Antonio-Balestrino/Bluetooth-Speaker-Senior-Design/docs/Kicad Files/Power Distribution Jack/PD Jack_RevB/3D View Bottom.jpg

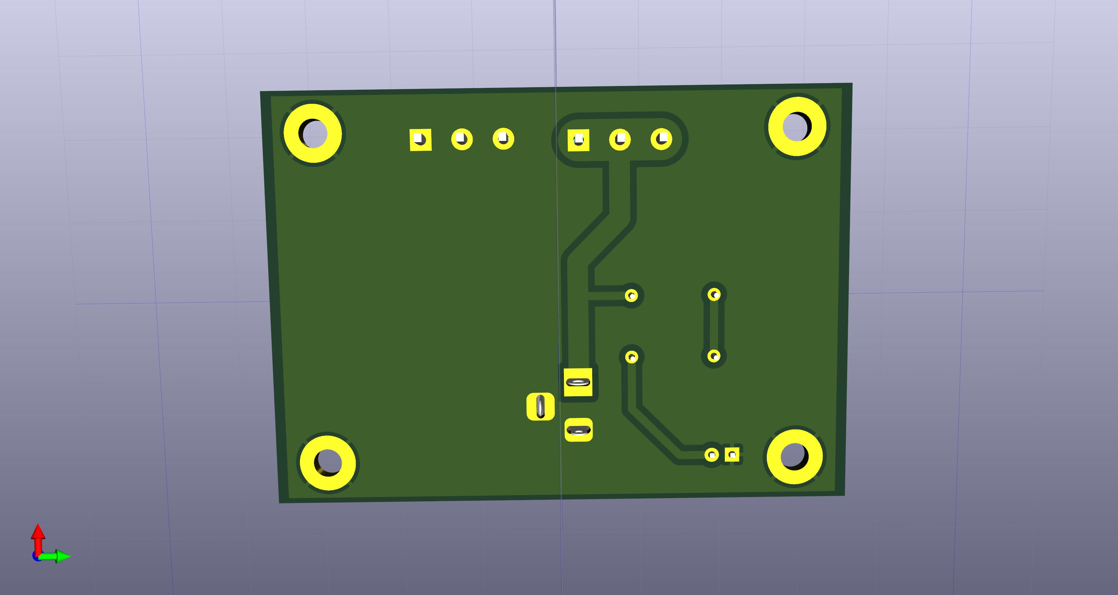
docs/Kicad Files/Power Distribution Jack/PD Jack_RevB/3D View Bottom.jpg
