Antonio-Balestrino/Bluetooth-Speaker-Senior-Design/docs/Pics/IMG_7961.JPG

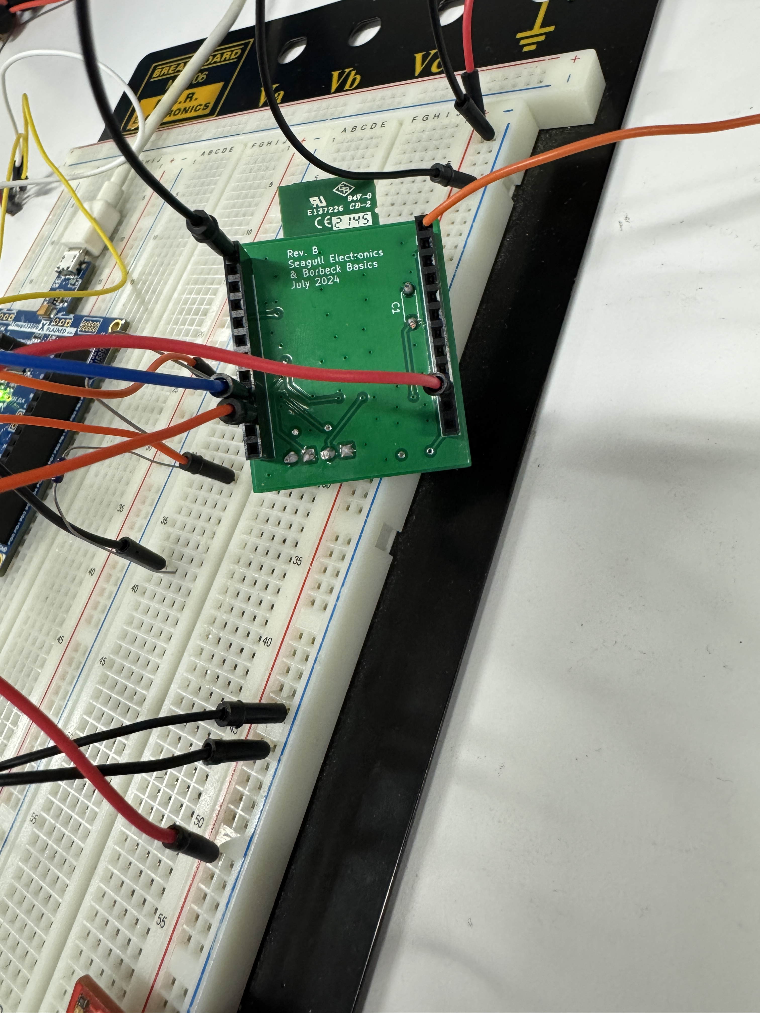
docs/Pics/IMG_7961.JPG
