Antonio-Balestrino/Bluetooth-Speaker-Senior-Design/docs/Pics/IMG_7962.JPG

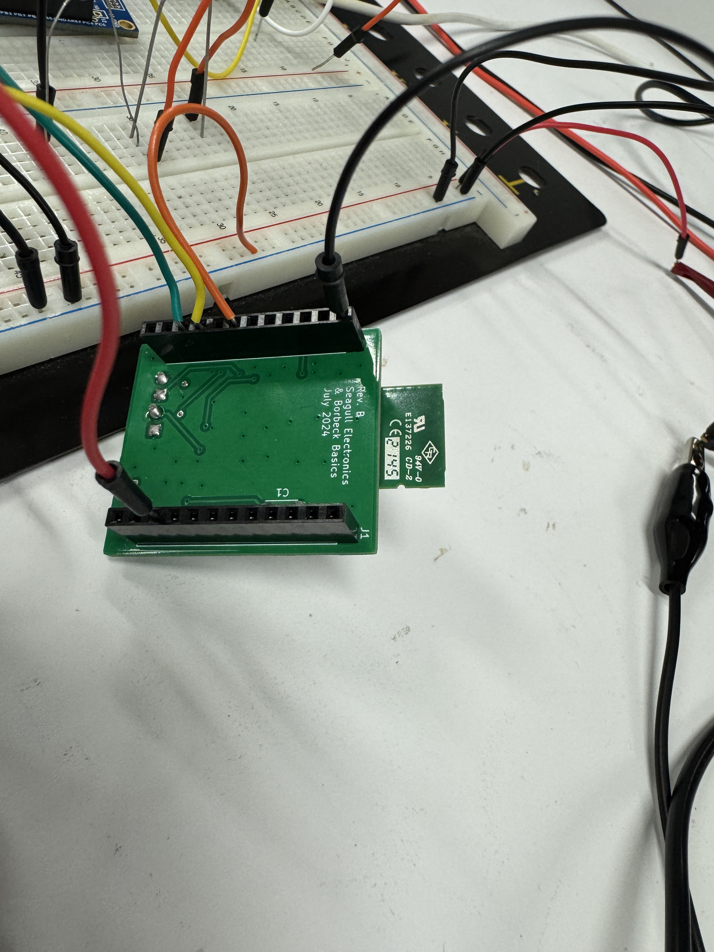
docs/Pics/IMG_7962.JPG
