Antonio-Balestrino/Bluetooth-Speaker-Senior-Design/docs/Pics/IMG_8013(1).JPG

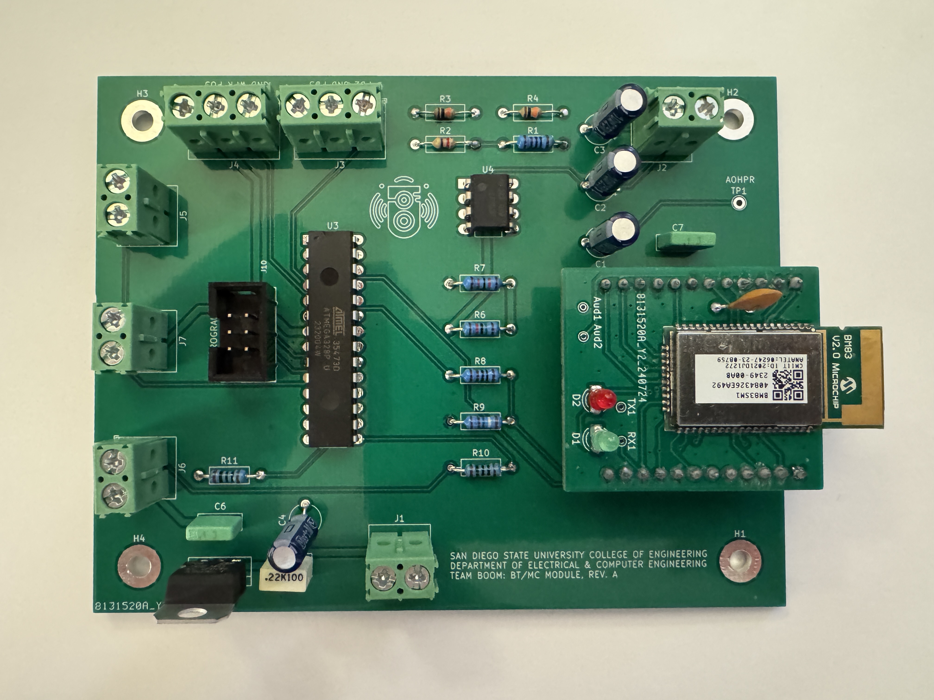
docs/Pics/IMG_8013(1).JPG
