Antonio-Balestrino/Bluetooth-Speaker-Senior-Design/docs/Pics/IMG_8014.JPG

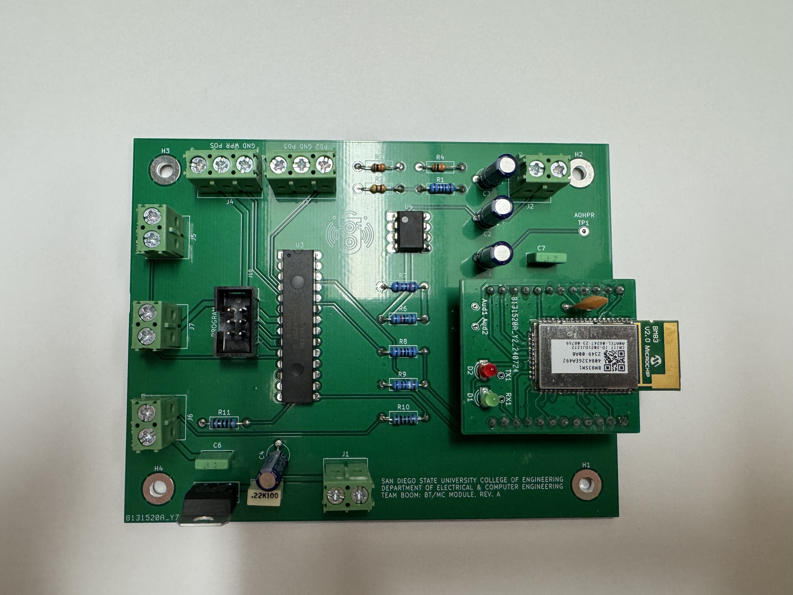
docs/Pics/IMG_8014.JPG
