Antonio-Balestrino/Bluetooth-Speaker-Senior-Design/docs/Pics/IMG_8023.JPG

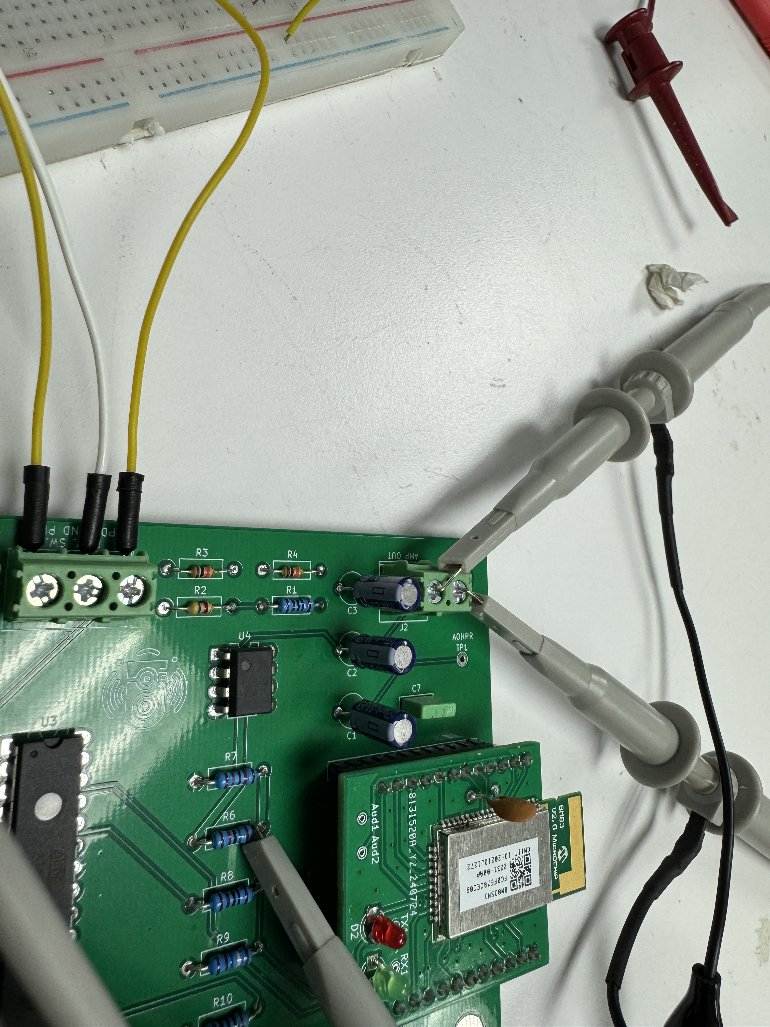
docs/Pics/IMG_8023.JPG
