Antonio-Balestrino/Bluetooth-Speaker-Senior-Design/docs/Pics/IMG_8121.JPG

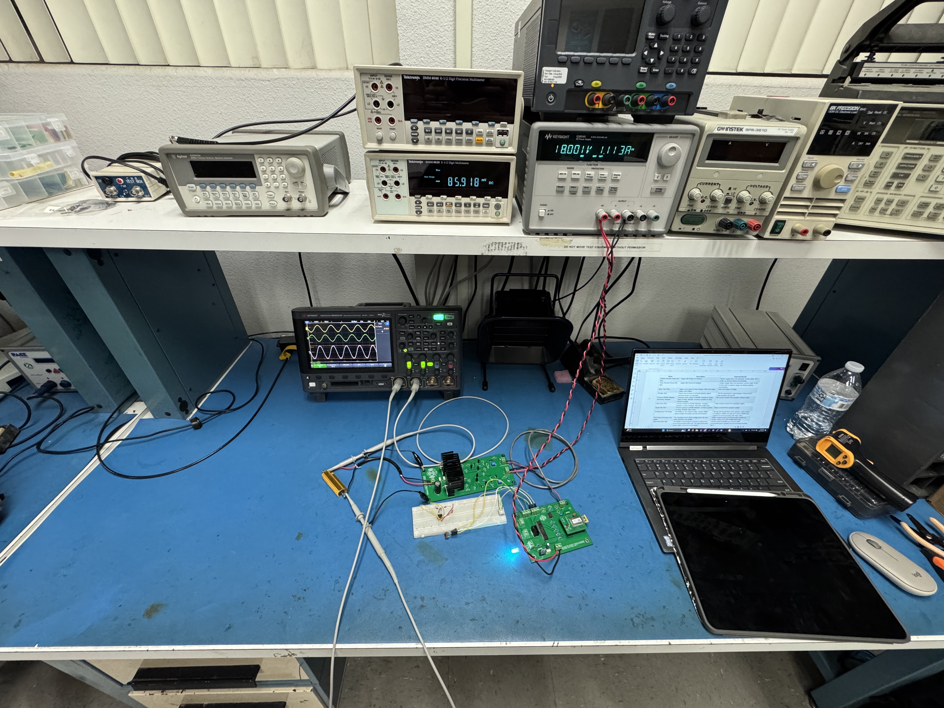
docs/Pics/IMG_8121.JPG
