Antonio-Balestrino/Bluetooth-Speaker-Senior-Design/docs/Pics/IMG_8177.JPG

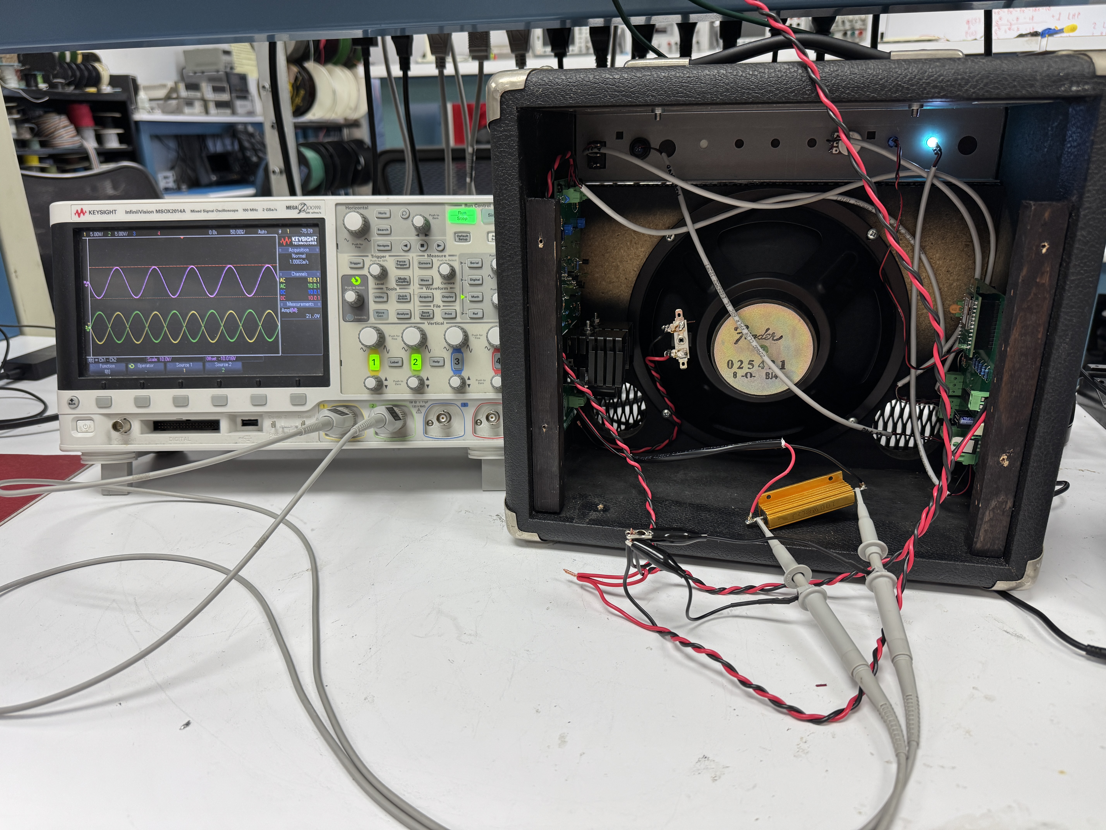
docs/Pics/IMG_8177.JPG
