Antonio-Balestrino/Bluetooth-Speaker-Senior-Design/docs/Pics/IMG_8189.JPG

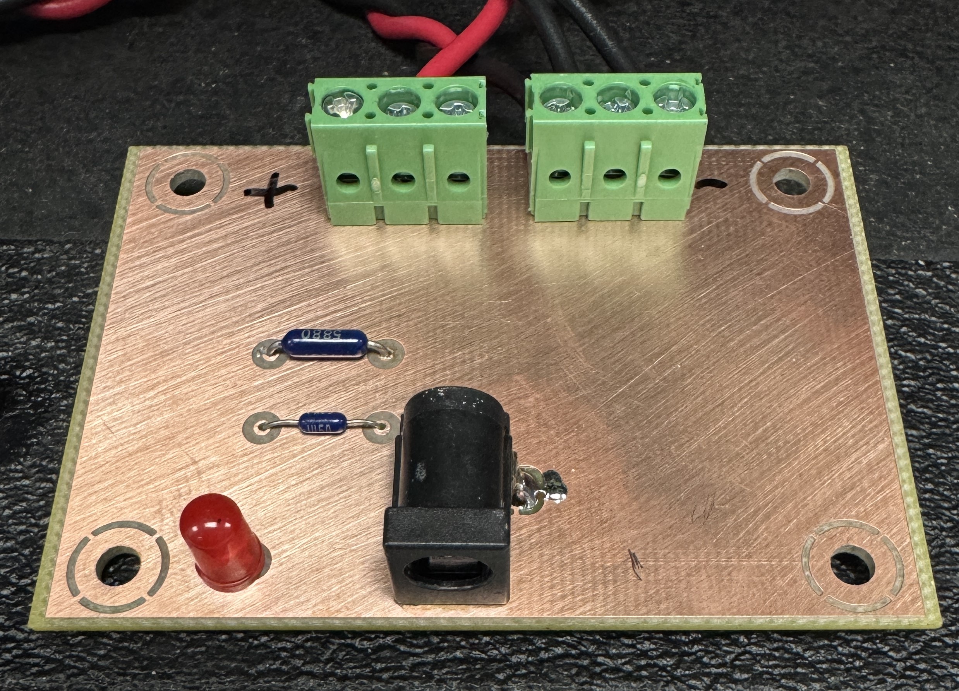
docs/Pics/IMG_8189.JPG
