Antonio-Balestrino/Bluetooth-Speaker-Senior-Design/docs/Pics/IMG_8190.JPG

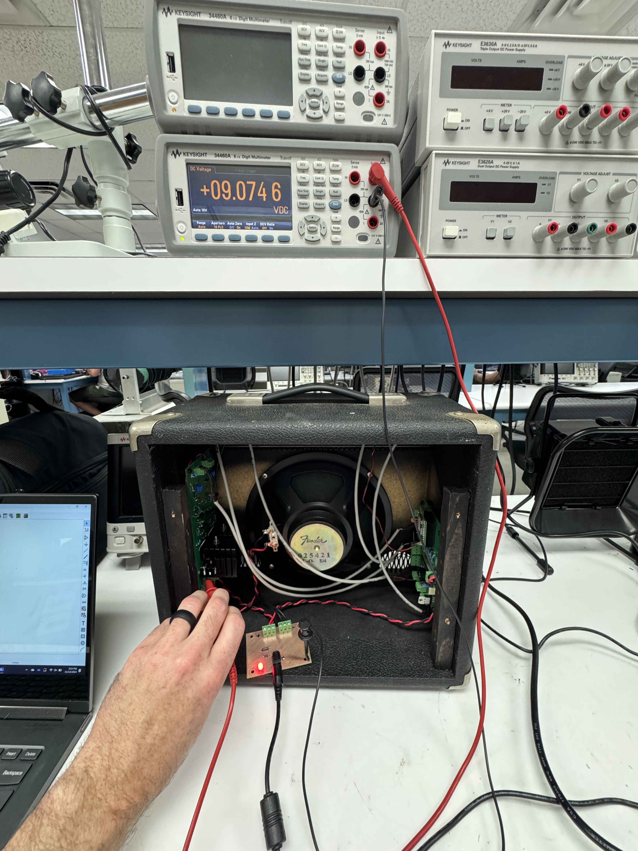
docs/Pics/IMG_8190.JPG
