Antonio-Balestrino/Bluetooth-Speaker-Senior-Design/docs/Pics/IMG_8191.JPG

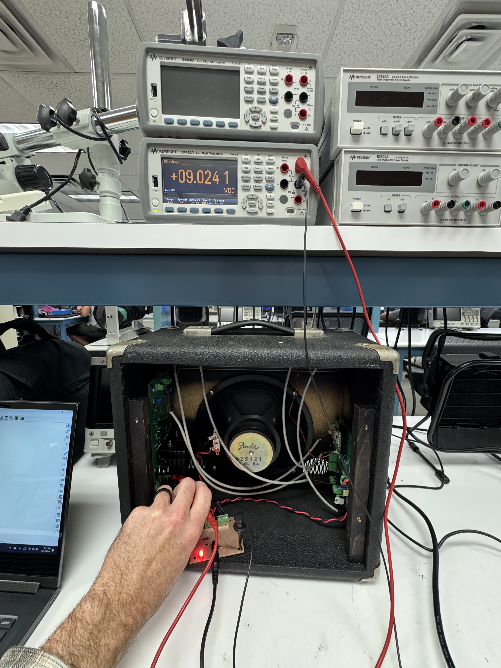
docs/Pics/IMG_8191.JPG
