Antonio-Balestrino/Bluetooth-Speaker-Senior-Design/docs/Pics/IMG_8192.JPG

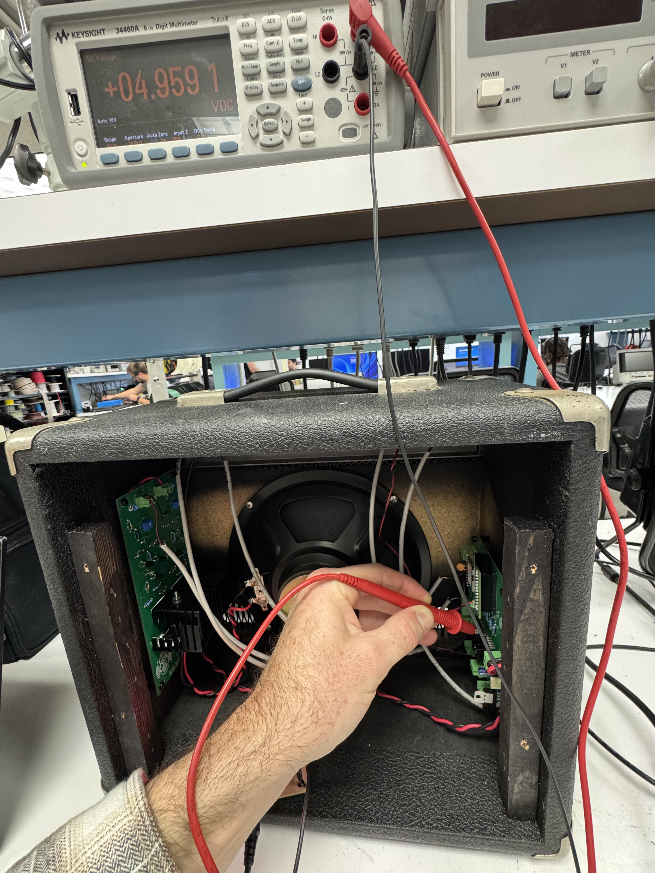
docs/Pics/IMG_8192.JPG
