Antonio-Balestrino/Bluetooth-Speaker-Senior-Design/docs/Pics/IMG_8193.JPG

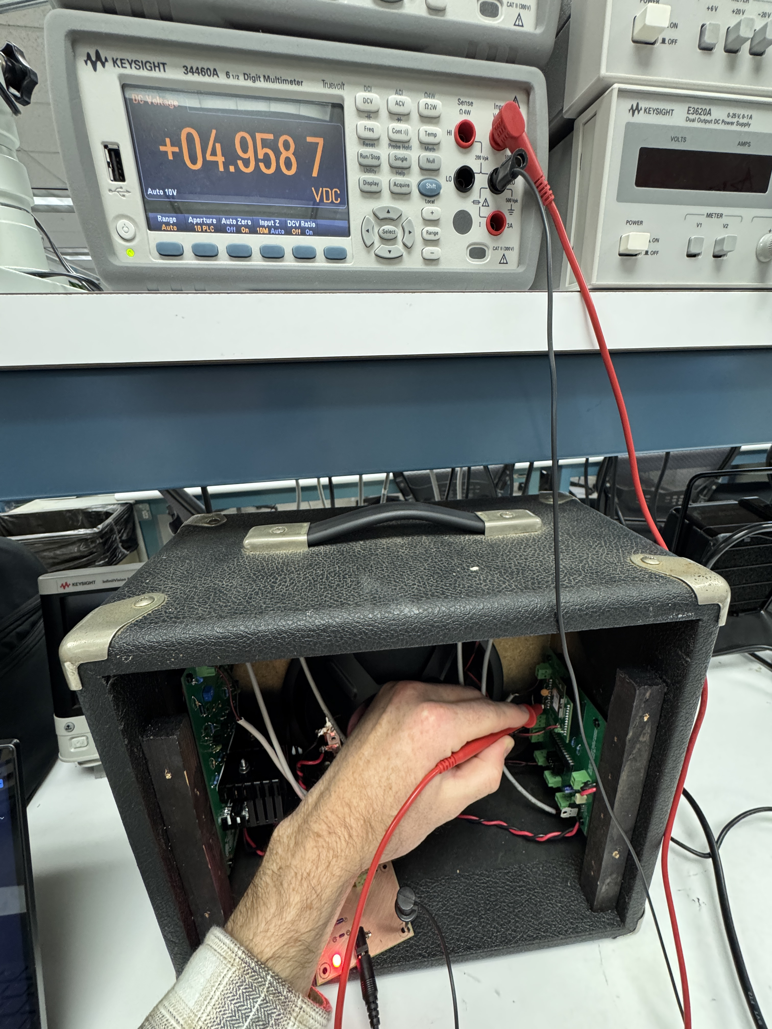
docs/Pics/IMG_8193.JPG
