Antonio-Balestrino/Bluetooth-Speaker-Senior-Design/docs/Pics/IMG_8194.JPG

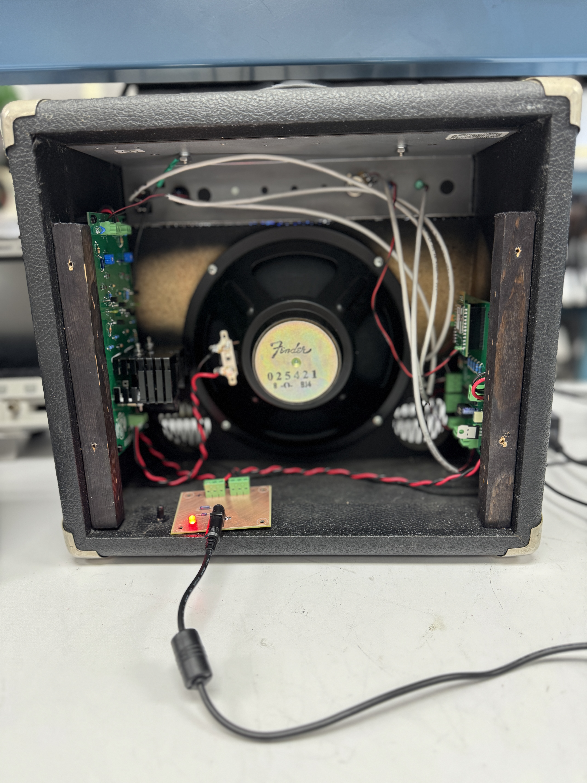
docs/Pics/IMG_8194.JPG
