Antonio-Balestrino/Bluetooth-Speaker-Senior-Design/docs/Scope Captures/scope_0.bmp

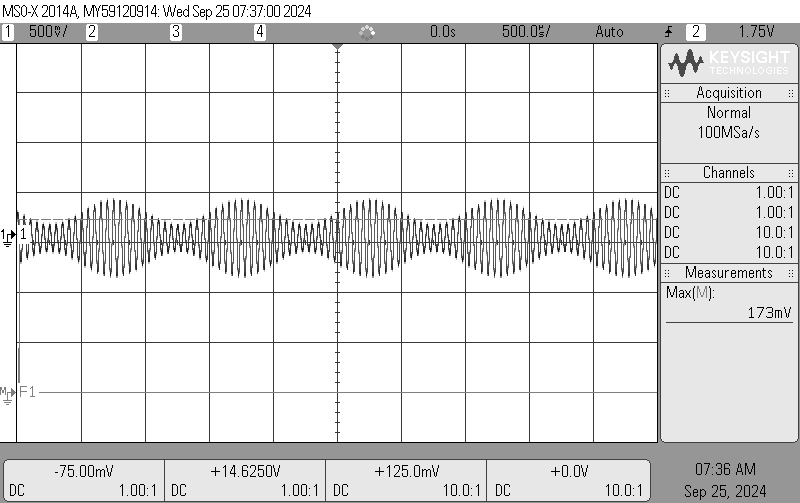
docs/Scope Captures/scope_0.bmp
