Antonio-Balestrino/Bluetooth-Speaker-Senior-Design/docs/Scope Captures/scope_1.bmp

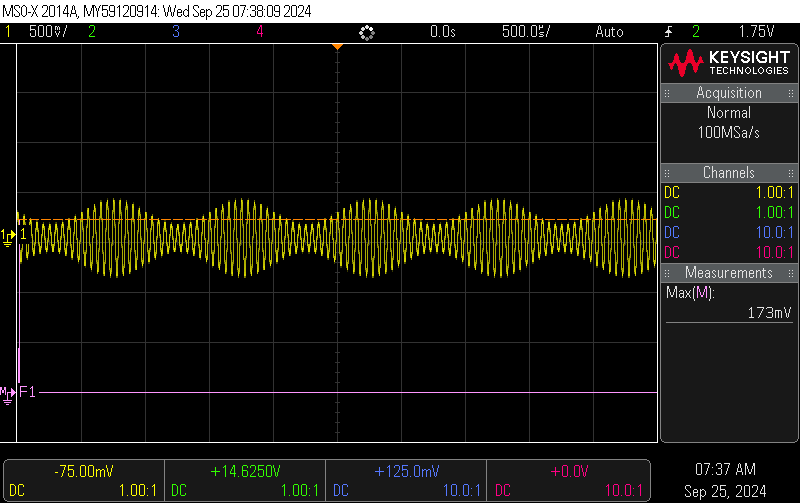
docs/Scope Captures/scope_1.bmp
