Antonio-Balestrino/Bluetooth-Speaker-Senior-Design/docs/Scope Captures/scope_5.png

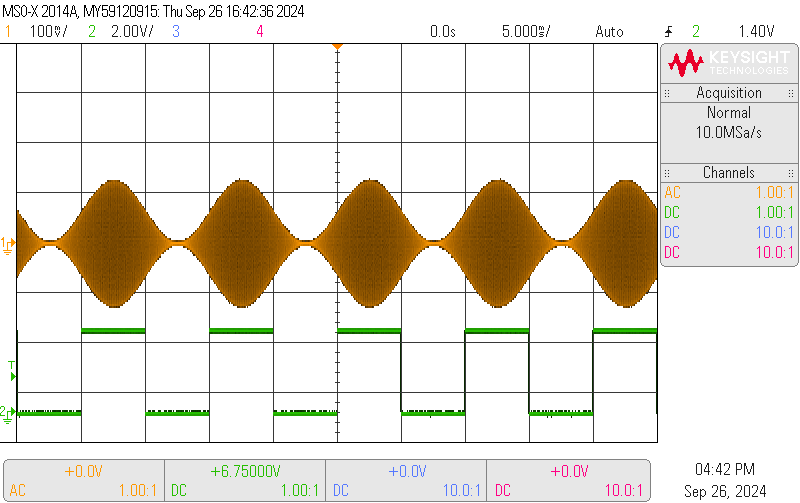
docs/Scope Captures/scope_5.png
