Antonio-Balestrino/Bluetooth-Speaker-Senior-Design/docs/Scope Captures/scope_6.png

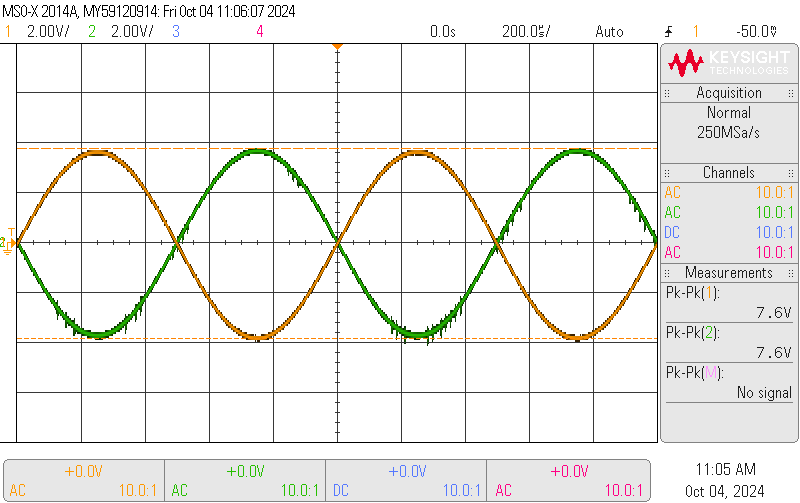
docs/Scope Captures/scope_6.png
