Antonio-Balestrino/Bluetooth-Speaker-Senior-Design/docs/Scope Captures/scope_7.png

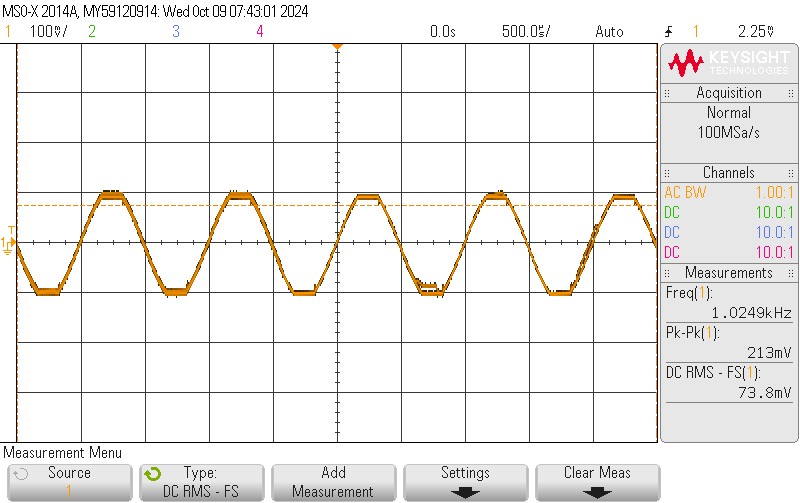
docs/Scope Captures/scope_7.png
