Antonio-Balestrino/Bluetooth-Speaker-Senior-Design/docs/Scope Captures/scope_8.png

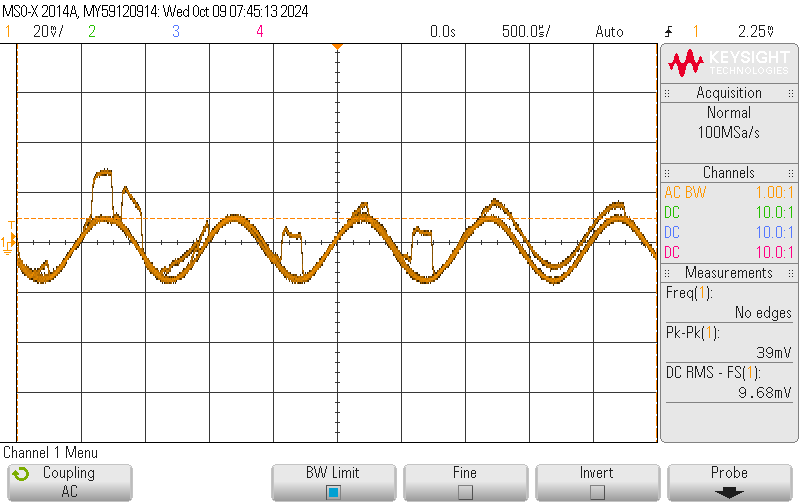
docs/Scope Captures/scope_8.png
