Antonio-Balestrino/Bluetooth-Speaker-Senior-Design/docs/Scope Captures/scope_9.png

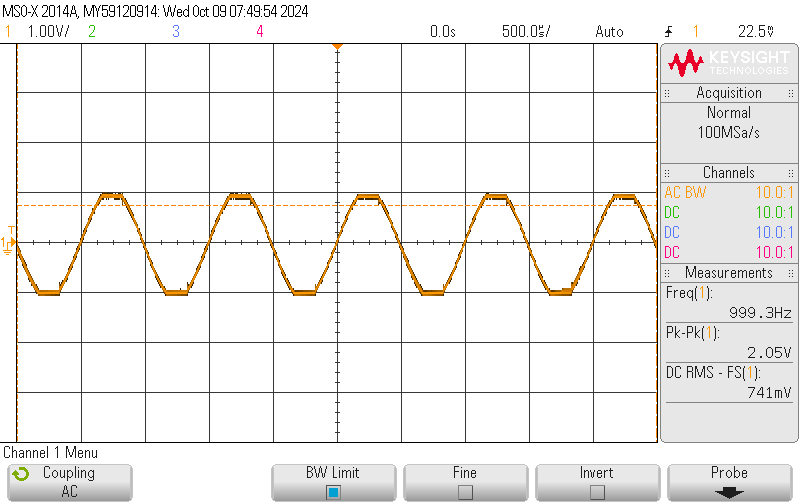
docs/Scope Captures/scope_9.png
