Antonio-Balestrino/Bluetooth-Speaker-Senior-Design/docs/Scope Captures/scope_13.png

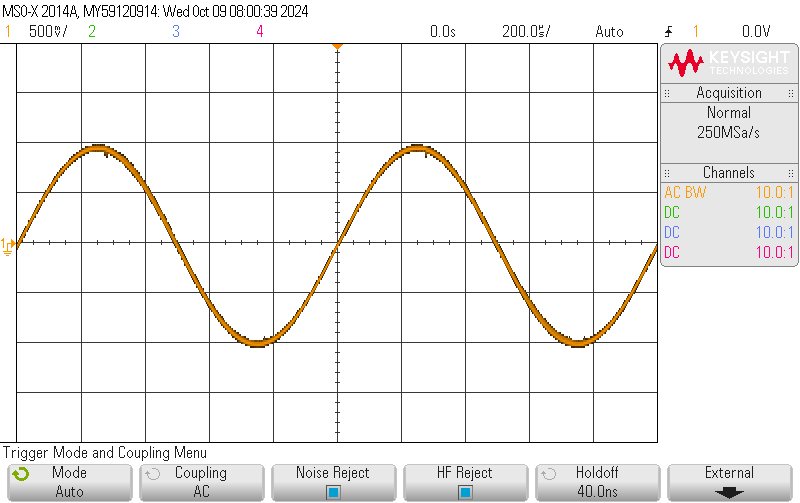
docs/Scope Captures/scope_13.png
