Antonio-Balestrino/Bluetooth-Speaker-Senior-Design/docs/Scope Captures/scope_14.png

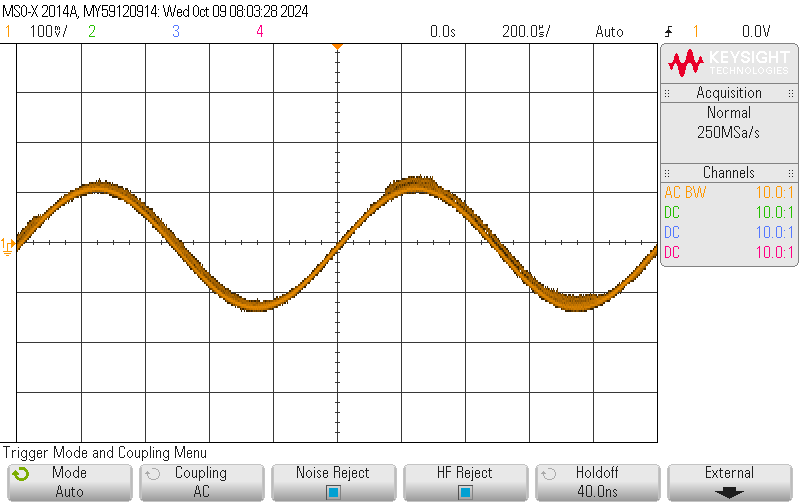
docs/Scope Captures/scope_14.png
