Antonio-Balestrino/Bluetooth-Speaker-Senior-Design/docs/Scope Captures/scope_15.png

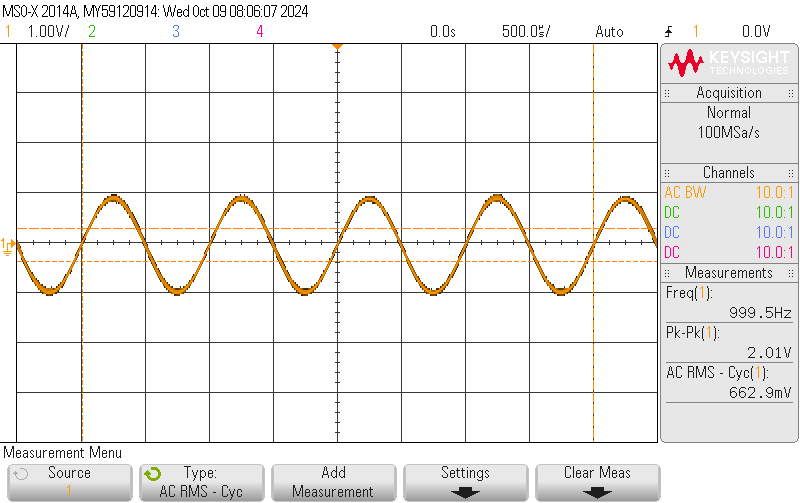
docs/Scope Captures/scope_15.png
