Antonio-Balestrino/Bluetooth-Speaker-Senior-Design/docs/Scope Captures/scope_16.png

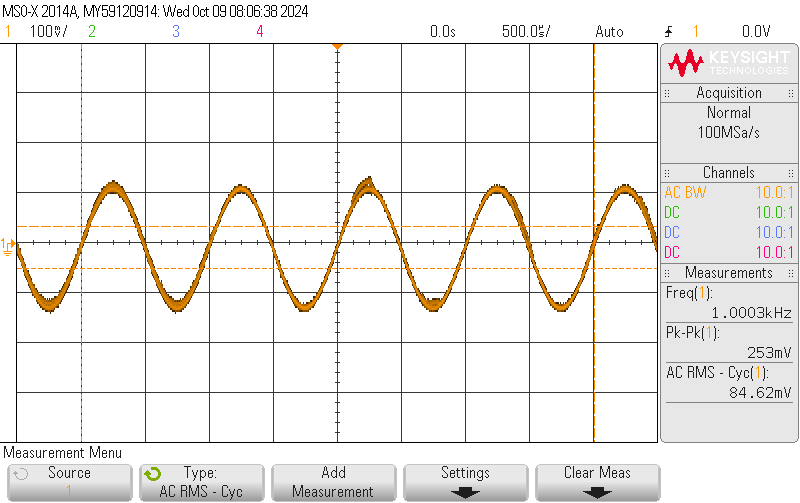
docs/Scope Captures/scope_16.png
