Antonio-Balestrino/Bluetooth-Speaker-Senior-Design/docs/Scope Captures/scope_19.png

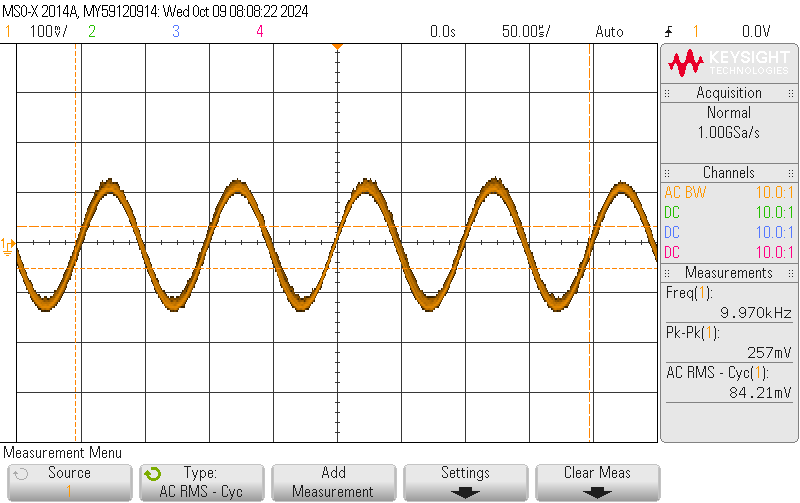
docs/Scope Captures/scope_19.png
