Antonio-Balestrino/Bluetooth-Speaker-Senior-Design/docs/THD Scope Captures/scope_0 - 10k 6%.png

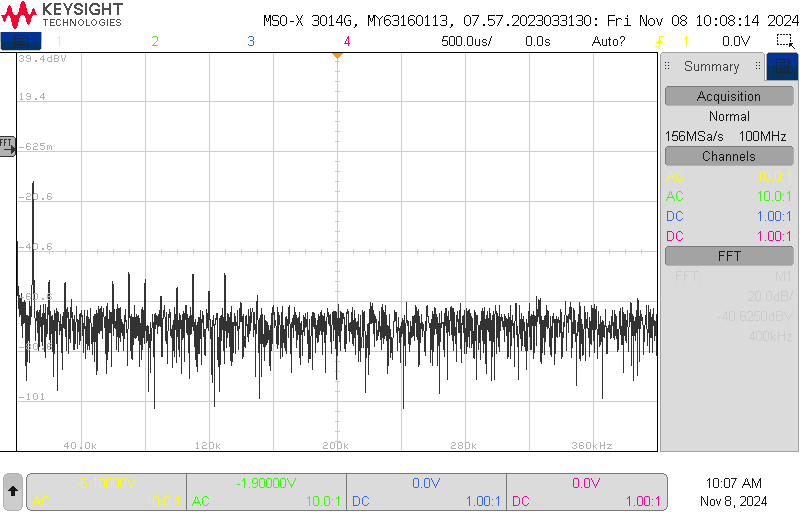
docs/THD Scope Captures/scope_0 - 10k 6%.png
