Antonio-Balestrino/Bluetooth-Speaker-Senior-Design/docs/THD Scope Captures/scope_1 - 10k 25%.png

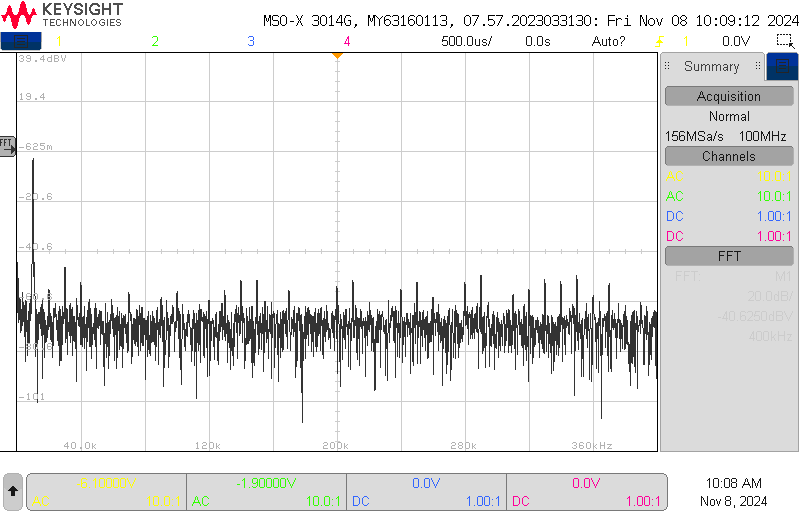
docs/THD Scope Captures/scope_1 - 10k 25%.png
