Antonio-Balestrino/Bluetooth-Speaker-Senior-Design/docs/THD Scope Captures/scope_2 - 10k 50%.png

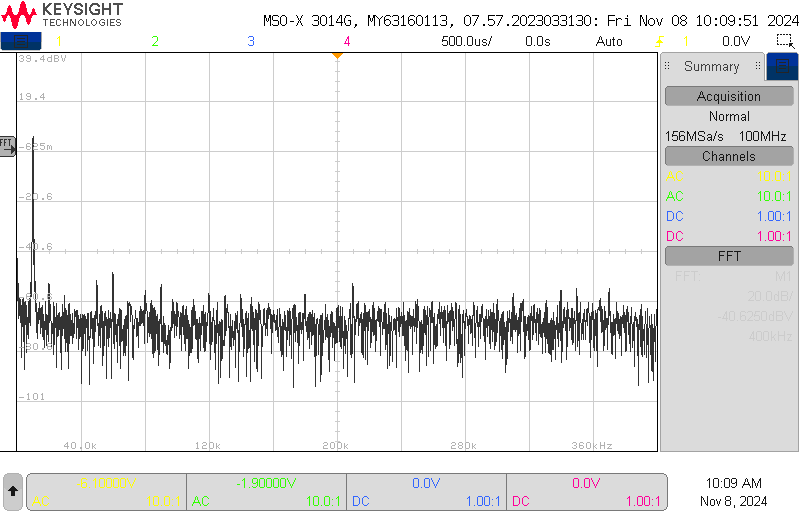
docs/THD Scope Captures/scope_2 - 10k 50%.png
