Antonio-Balestrino/Bluetooth-Speaker-Senior-Design/docs/THD Scope Captures/scope_4 - 10k 100%.png

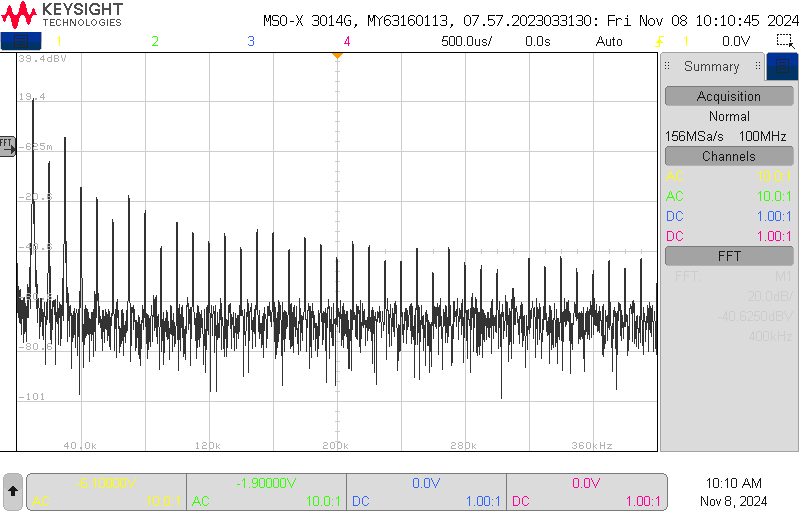
docs/THD Scope Captures/scope_4 - 10k 100%.png
