Antonio-Balestrino/Bluetooth-Speaker-Senior-Design/docs/Kicad Files/Amplifier/Power_Amp_RevB/STEP/Power_Amp_RevB.png

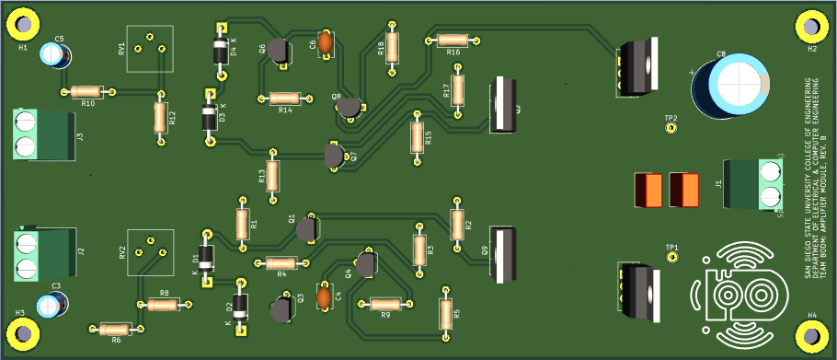
docs/Kicad Files/Amplifier/Power_Amp_RevB/STEP/Power_Amp_RevB.png
