Antonio-Balestrino/Bluetooth-Speaker-Senior-Design/docs/Kicad Files/BM83_Carrier_Board/STEP/BM-83 Carrier PCB.png

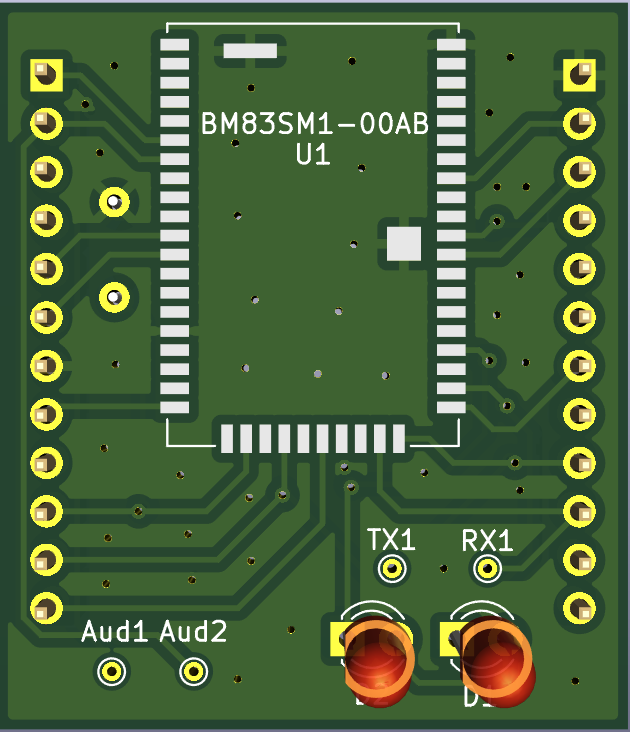
docs/Kicad Files/BM83_Carrier_Board/STEP/BM-83 Carrier PCB.png
