Antonio-Balestrino/Bluetooth-Speaker-Senior-Design/docs/System Test Scope Captures/scope_0.png

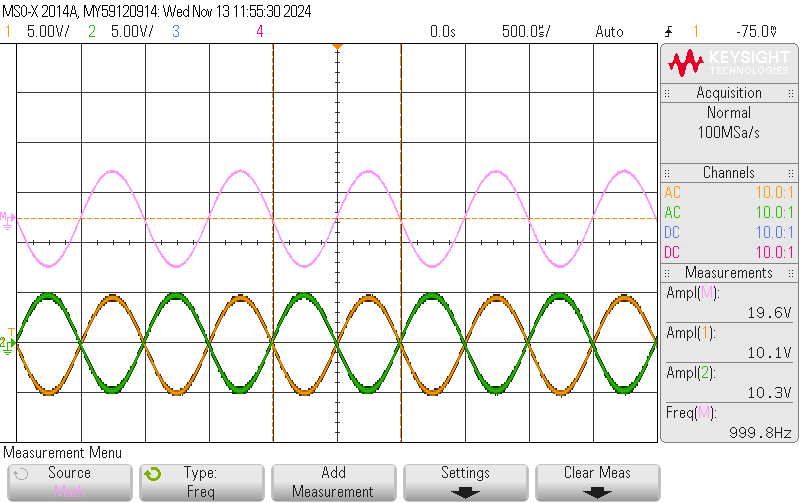
docs/System Test Scope Captures/scope_0.png
