Antonio-Balestrino/Bluetooth-Speaker-Senior-Design/docs/System Test Scope Captures/scope_1.png

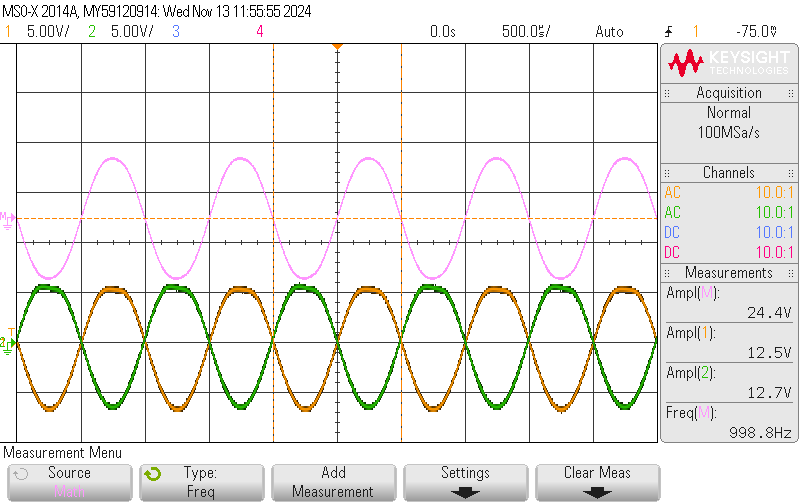
docs/System Test Scope Captures/scope_1.png
