Antonio-Balestrino/Bluetooth-Speaker-Senior-Design/docs/LTSPice Schematics/Power Distribution Jack/PD Jack.asc

D1: LED
R1: res; 700
R2: res; 200
V1: voltage; 18
Named nets: 0
.op
