Antonio-Balestrino/Bluetooth-Speaker-Senior-Design/docs/LTSPice Schematics/Amplifier/Dorr_full_RevA.asc

C1: cap; 0.22µF
C3: cap; 1µF
C4: cap; 1nF
C5: cap; 1µF
C6: cap; 1nF
C7: cap; 0.22µF
C8: cap; 1000µF
D1: diode; 1N4148
D2: diode; 1N4148
D3: diode; 1N4148
D4: diode; 1N4148
Q1: npn2; 2N3904
Q2: pnp2; QD45H8
Q3: npn2; 2N3904
Q4: pnp2; 2N3906
Q5: npn2; QD44H8
Q6: npn2; 2N3904
Q7: npn2; 2N3904
Q8: pnp2; 2N3906
Q9: pnp2; QD45H8
Q10: npn2; QD44H8
R1: res; 4.7k
R2: res; 10k
R3: res; 0.22
R4: res; 12k
R5: res; 0.22
R6: res; 4.7k
R8: res; 1.3k
R9: res; 10k
R10: res; 4.7k
R12: res; 1.3k
R13: res; 4.7k
R14: res; 12k
R15: res; 10k
R16: res; 10k
R17: res; 0.22
R18: res; 0.22
RV1: res; 3.8k
RV2: res; 3.8k
Speaker: res; 8
V1: voltage; SINE(8.5 2.3 100)
V2: voltage; 18
V3: voltage; SINE(8.5 2.3 100)
Named nets: 0, Speaker+, Input, 18V, Speaker-
.tran 1
.inc MMBT3904.lib
.inc D45h8.lib
.inc D44H8.lib
Note: Input should be ~1V Amplitude
