Antonio-Balestrino/Bluetooth-Speaker-Senior-Design/docs/LTSPice Schematics/ATmega_BM83/Voltage_Divider.asc

R1: res; 15k
R2: res; 12k
V1: voltage; 18
Named nets: 0
.tran 1
