Antonio-Balestrino/Bluetooth-Speaker-Senior-Design/docs/LTSPice Schematics/Amplifier/Dorr_half_circuit.asc

C1: cap; 1µF
C2: cap; 0.22µF
C3: cap; 1000µF
C4: cap; 1nF
D1: diode; 1N4148
D2: diode; 1N4148
Q5: npn2; 2N3904
Q7: npn2; 2N3904
Q8: pnp2; 2N3906
Q11: pnp2; QD45H8
Q12: npn2; QD44H8
R1: res; 2.2k
R2: res; 4.7k
R3: res; 10k
R4: res; 4.7k
R5: res; 5k
R6: res; 1.3k
R7: res; 0.22
R8: res; 12k
R9: res; 0.22
R10: res; 8
R: res; 10k
V1: voltage; SINE(0 1 1k)
V2: voltage; 18
Named nets: 0, Speaker+, Input, Mute_Input, 18V
.tran 1
.inc MMBT3904.lib
.inc D45h8.lib
.inc D44H8.lib
