Antonio-Balestrino/Bluetooth-Speaker-Senior-Design/docs/LTSPice Schematics/Amplifier/insta_50W.asc

C1: cap; 300p
D1: LED
Input: voltage; SINE(0 1mv 20k)
Q1: pnp; 2N5401
Q2: pnp; 2N5401
Q3: pnp; 2N5401
Q4: npn
Q5: pnp
Q6: pnp; 2N5401
Q7: pnp; 2N5401
R1: res; 1k
R2: res; 1k
R3: res; 19k
R4: res; 33k
R5: res; 590
R6: res; 22
R7: res; 518
R8: res; 1.2k
R9: res; 62
R10: res; 33k
R11: res; 33
R12: res; 33
R13: res; 0.33
R14: res; 0.33
U1: 2n5551
U2: 2n5551
V1: voltage; 35
V2: voltage; 35
Named nets: 0, 35V, Out, -35V
.tran 5ms
