Antonio-Balestrino/Bluetooth-Speaker-Senior-Design/docs/LTSPice Schematics/Amplifier/op_amps.asc

C1: cap; 1000µ
Input: voltage; SINE(9 700mv 20k)
Speaker: res; 8
U1: OP747
U2: OP747
VCC: voltage; 18
Named nets: VCC, 0, Out, Input
.tran 10
