Antonio-Balestrino/Bluetooth-Speaker-Senior-Design/docs/Kicad Files/Amplifier/Amplifier/Amplifier, REV-/Current_Calc/Current_Calc/Dorr_full_RevA.asc

C1: cap; 1µF
C2: cap; 0.22µF
C3: cap; 1000µF
C4: cap; 1nF
C5: cap; 1µF
C6: cap; 0.22µF
C8: cap; 1nF
D1: diode; 1N4148
D2: diode; 1N4148
D3: diode; 1N4148
D4: diode; 1N4148
Q1: npn2; 2N3904
Q2: npn2; 2N3904
Q3: pnp2; QD45H8
Q4: npn2; QD44H8
Q5: npn2; 2N3904
Q6: pnp2; 2N3906
Q7: npn2; 2N3904
Q8: pnp2; 2N3906
Q11: pnp2; QD45H8
Q12: npn2; QD44H8
R1: res; 00.0001
R2: res; 4.7k
R3: res; 10k
R4: res; 4.7k
R5: res; 1.3k
R6: res; 3.8k
R7: res; 0.22
R8: res; 12k
R9: res; 0.22
R12: res; 4.7k
R13: res; 10k
R14: res; 4.7k
R15: res; 1.3k
R16: res; 3.8k
R17: res; 0.22
R18: res; 12k
R19: res; 0.22
R20: res; 10k
R: res; 10k
Speaker: res; 8
V1: voltage; SINE(0 2.5 100)
V2: voltage; 18
V3: voltage; SINE(0 2.5 100)
Named nets: 0, Speaker+, Input, 18V, Speaker-
.tran 1
.inc MMBT3904.lib
.inc D45h8.lib
.inc D44H8.lib
