Antonio-Balestrino/Bluetooth-Speaker-Senior-Design/docs/Pics/IMG_8179.JPG

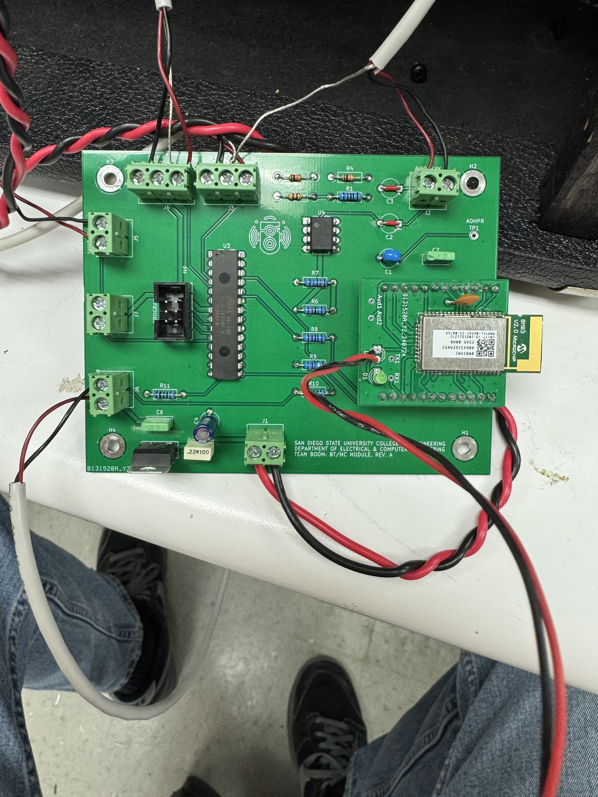
docs/Pics/IMG_8179.JPG
